brucemack/sdr2/docs/IMG_1789.jpg

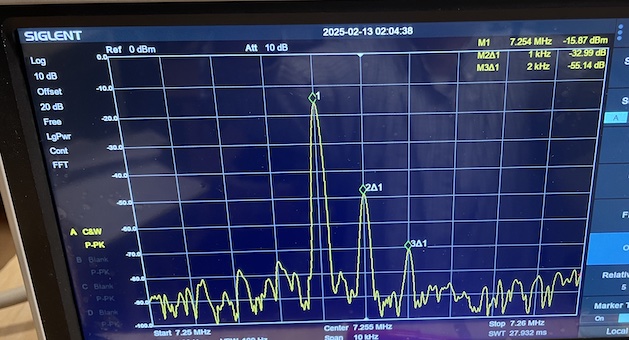
docs/IMG_1789.jpg
