brucemack/sdr2/hw/tx-1/plots/tx-1.pdf

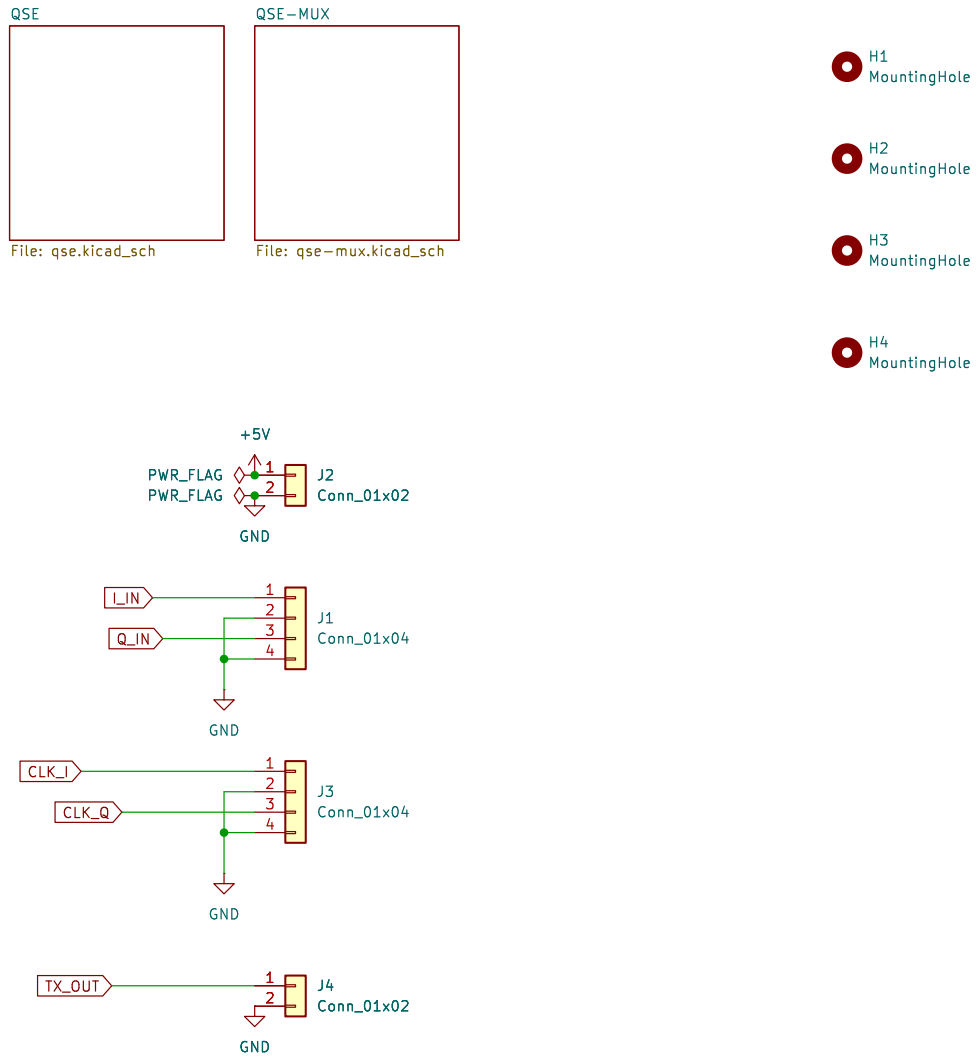
[picture p18: page 1]

H3 MountingHole H2 MountingHole H1 MountingHole GND GND

Id: 1/3 Title: Quadrature Transmit Board

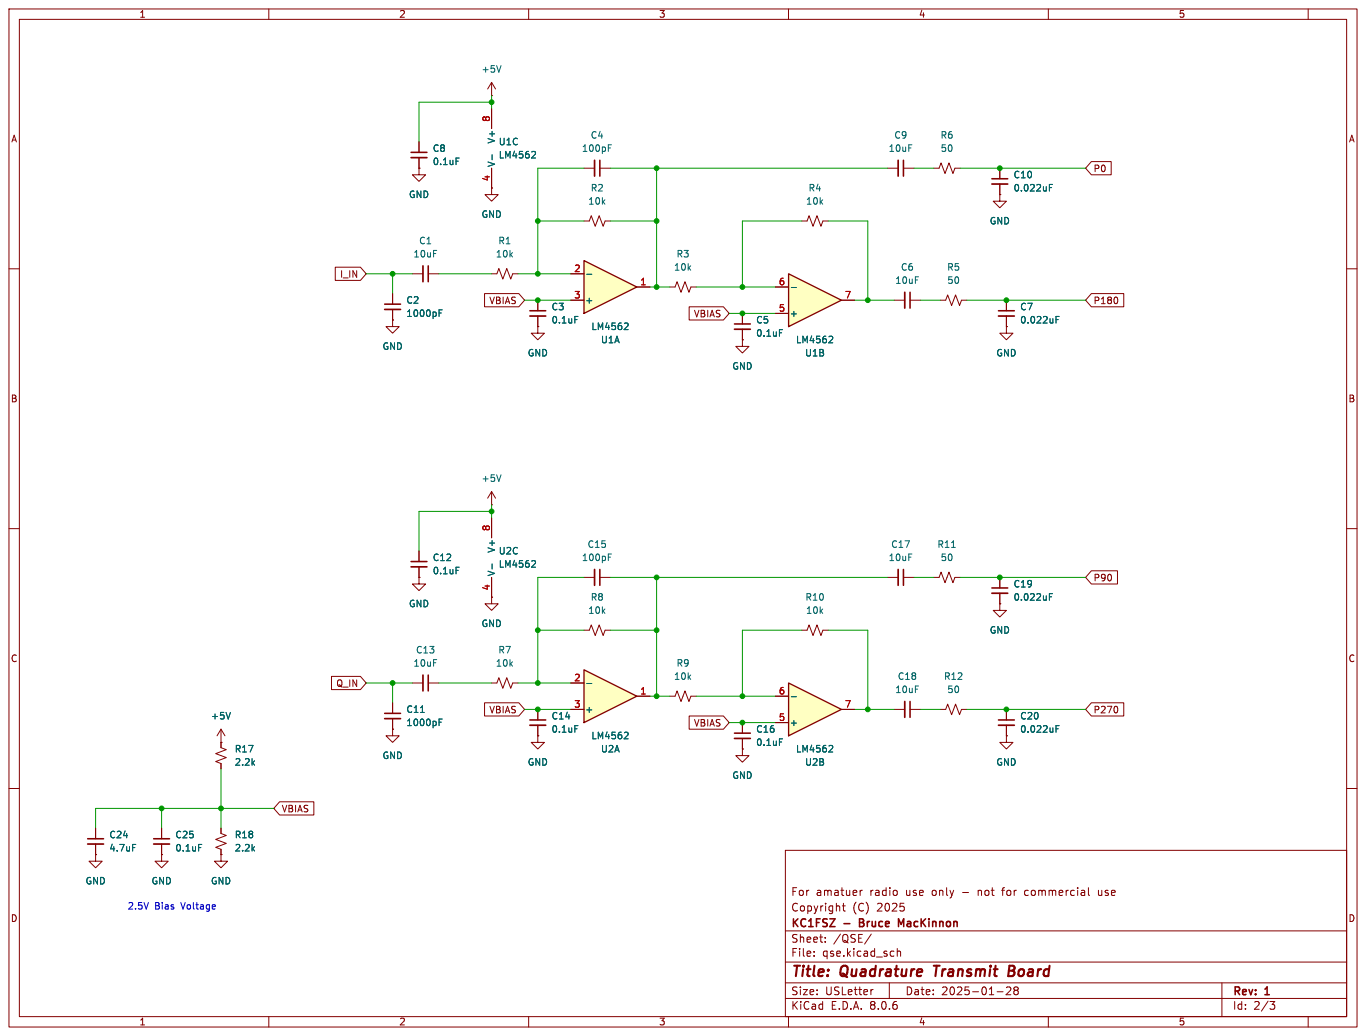
[picture p19: page 2]

Id: 2/3 Title: Quadrature Transmit Board

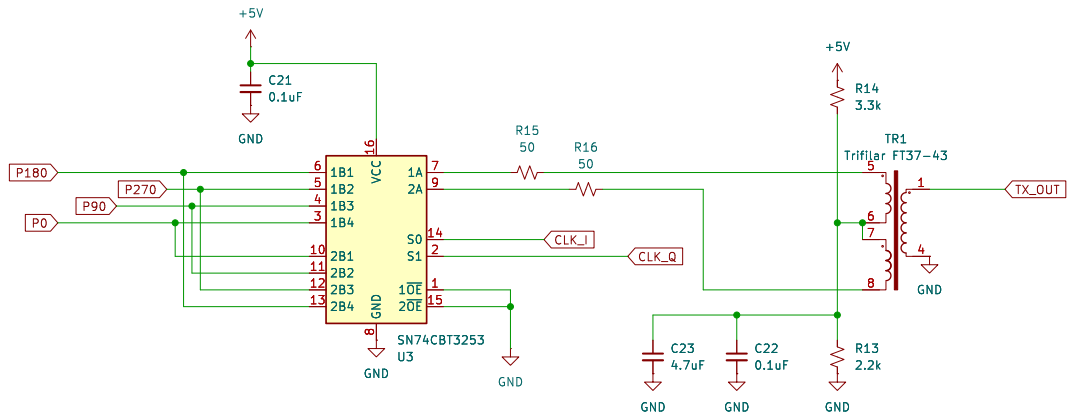
[picture p20: page 3]

Id: 3/3 Title: Quadrature Transmit Board
